BW25/Humber_Capstone/images/budget.PNG

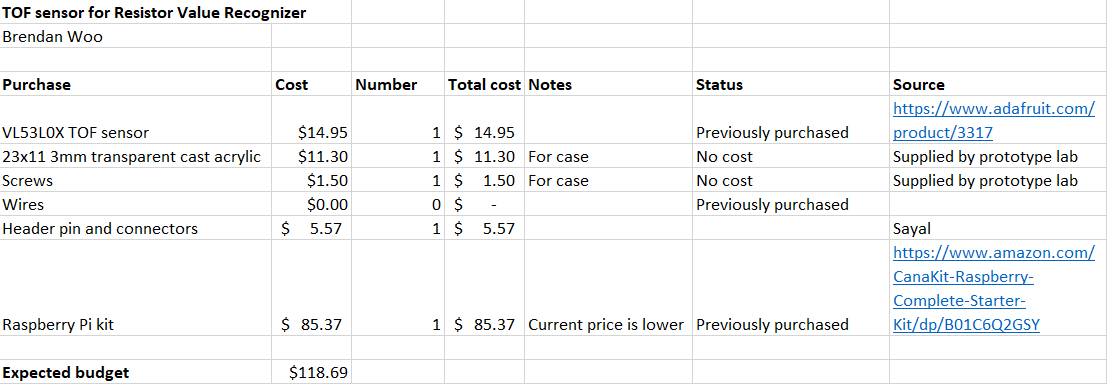
images/budget.PNG
