BW25/Humber_Capstone/images/Sensor.jpg

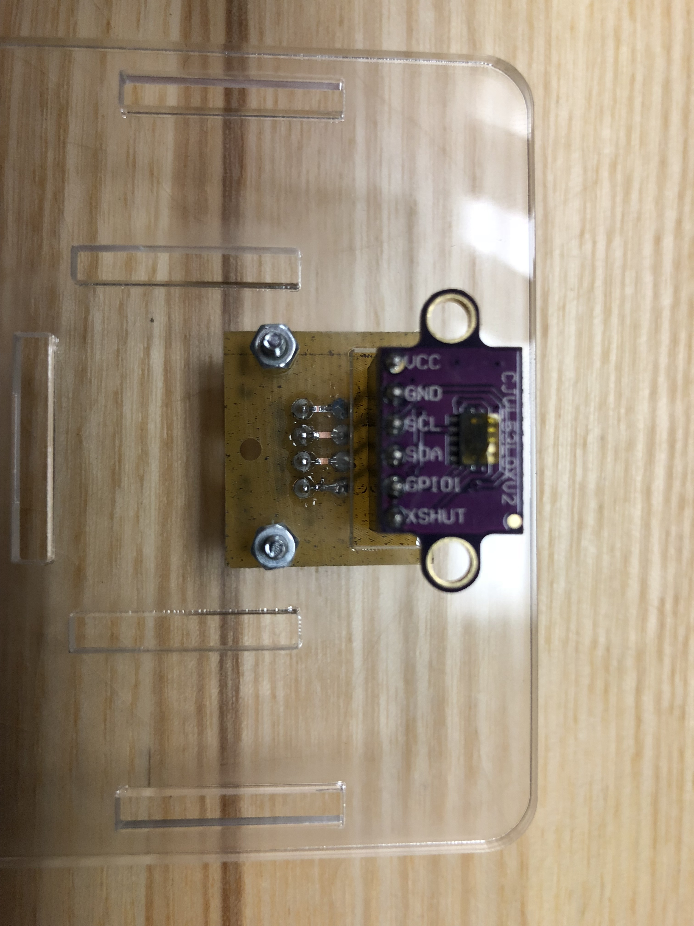
images/Sensor.jpg
